hazels-garage/satpad/output/art.png

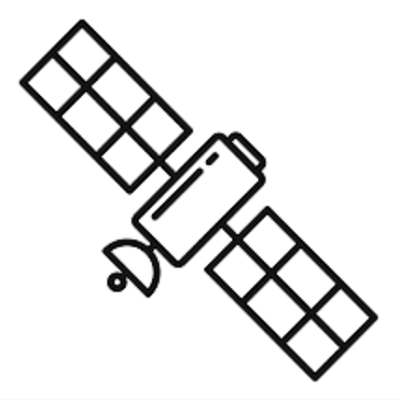
output/art.png
